nikito7/easyhan/misc/lorawan/README.md

# LoRaWAN / TTN

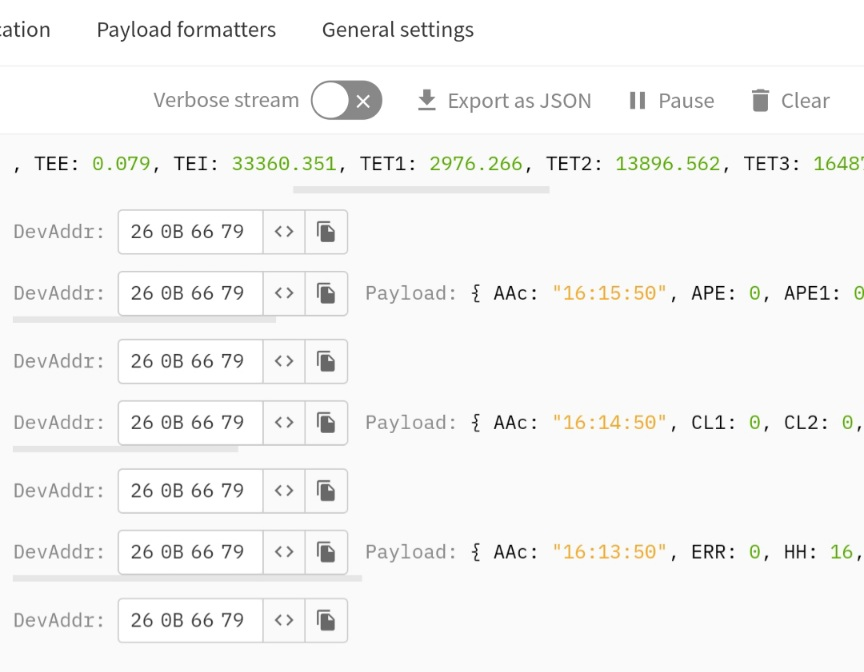
[picture p13: misc/lorawan/han/ttn-1.jpg]
ttn-1
