nikito7/easyhan/V1/esp32/README.md

ESP32 test

<hr>

```js
Backlog 
TimeZone 99; 
TimeDST 0,0,3,1,1,60; 
TimeSTD 0,0,10,1,2,0; 
MqttUser none; 
MqttPassword none; 
MqttClient Easy_HAN_32_%06X; 
WebLog 4; 
WifiPower 15; 
Topic edpbox99; 
Restart 1; ; 
```

```js
Backlog 
SSID2 edpbox2-dev; 
Password2 edpbox123; 
Hostname Easy-HAN-EB99-32; 
WifiConfig 2;
OtaUrl http://u.easyhan.pt/han/tasmota32.bin; 
Restart 1; ; 
```

---

2. 

Easy HAN

(linha única)

EOF
